CommPass357/Train-Models/models/up-80-coal-turbine/v1.0.4/exports/stl/shells/a_control_shell.stl

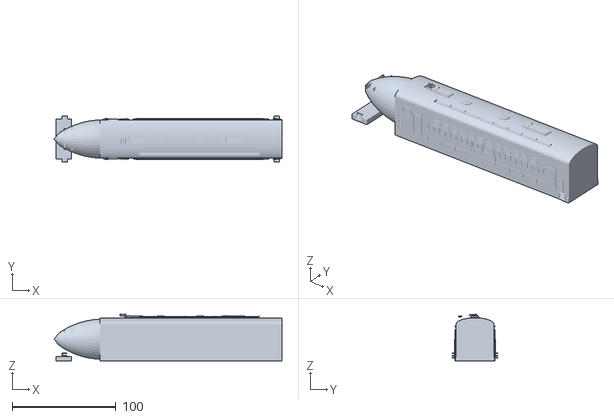
[picture p15: CAD file, 2026-04-26]
models/up-80-coal-turbine/v1.0.4/exports/stl/shells/a_control_shell.stl
219.4 x 44.0 x 45.1
