CommPass357/Train-Models/models/up-80-coal-turbine/v1.0.4/exports/stl/chassis_parts/center_turbine/center_turbine_shell_mount_boss_set.stl

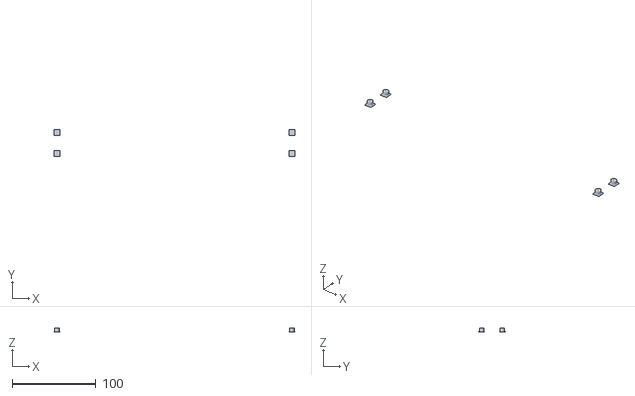
[picture p16: CAD file, 2026-04-26]
models/up-80-coal-turbine/v1.0.4/exports/stl/chassis_parts/center_turbine/center_turbine_shell_mount_boss_set.stl
287.2 x 31.7 x 4.40
