CommPass357/Train-Models/models/up-80-coal-turbine/v1.0.4/exports/stl/chassis_parts/coal_tender/coal_tender_cosmetic_sideframes.stl

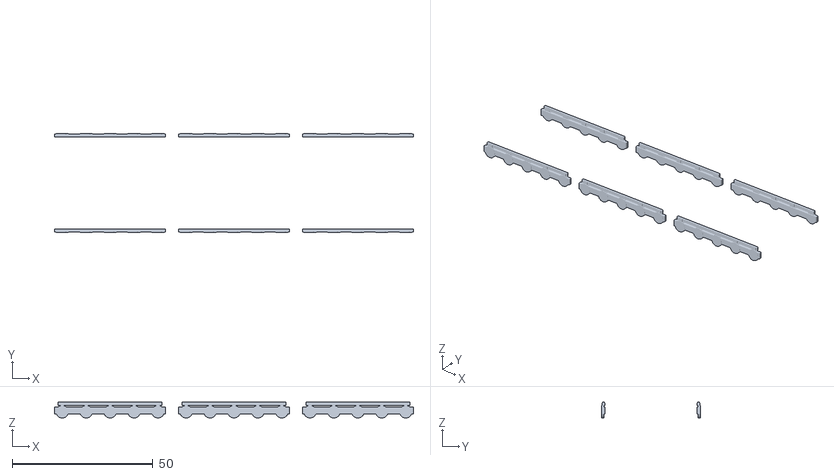
[picture p17: CAD file, 2026-04-26]
models/up-80-coal-turbine/v1.0.4/exports/stl/chassis_parts/coal_tender/coal_tender_cosmetic_sideframes.stl
127.5 x 35.0 x 5.67
