CommPass357/Train-Models/models/up-80-coal-turbine/v1.0.4/exports/stl/chassis_parts/a_control/a_control_truck_bolster_01.stl

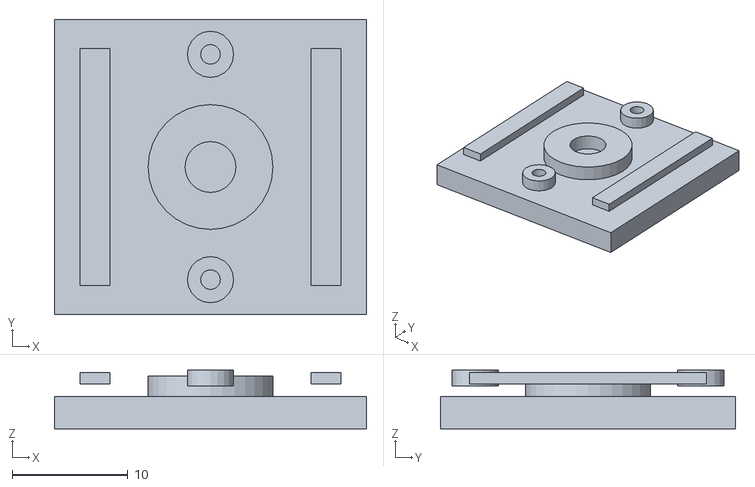
[picture p18: CAD file, 2026-04-26]
models/up-80-coal-turbine/v1.0.4/exports/stl/chassis_parts/a_control/a_control_truck_bolster_01.stl
27.0 x 25.5 x 5.10
