CommPass357/Train-Models/models/up-80-coal-turbine/v1.0.4/exports/stl/chassis_parts/coal_tender/coal_tender_wire_retainers.stl

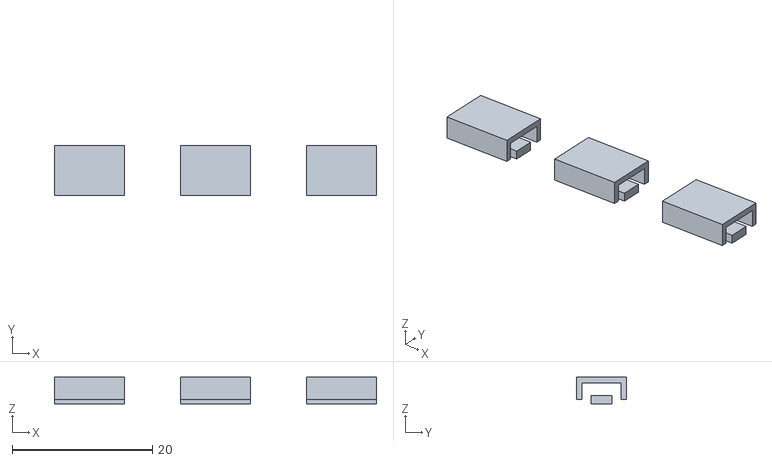
[picture p19: CAD file, 2026-04-26]
models/up-80-coal-turbine/v1.0.4/exports/stl/chassis_parts/coal_tender/coal_tender_wire_retainers.stl
46.0 x 7.20 x 3.80
