CommPass357/Train-Models/models/up-80-coal-turbine/v1.0.4/exports/stl/chassis_parts/coal_tender/coal_tender_decoder_tray.stl

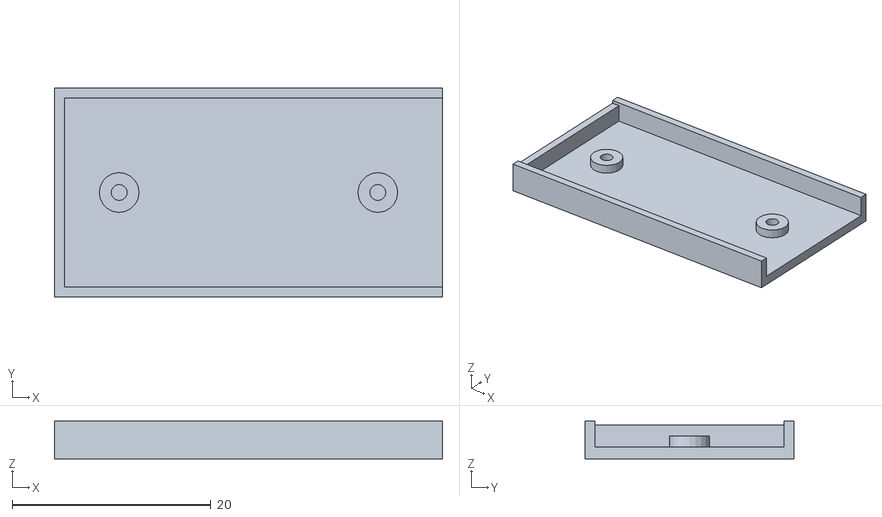
[picture p20: CAD file, 2026-04-26]
models/up-80-coal-turbine/v1.0.4/exports/stl/chassis_parts/coal_tender/coal_tender_decoder_tray.stl
39.0 x 21.0 x 3.80
