CommPass357/Train-Models/models/up-80-coal-turbine/v1.0.4/exports/stl/chassis_parts/coal_tender/coal_tender_pickup_wiper_mounts.stl

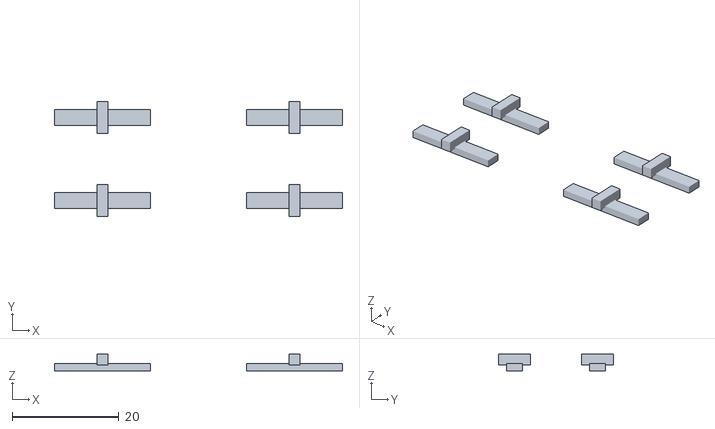
[picture p21: CAD file, 2026-04-26]
models/up-80-coal-turbine/v1.0.4/exports/stl/chassis_parts/coal_tender/coal_tender_pickup_wiper_mounts.stl
54.0 x 21.5 x 3.10
