CommPass357/Train-Models/models/up-80-coal-turbine/v1.0.4/exports/stl/chassis_parts/a_control/a_control_speaker_box.stl

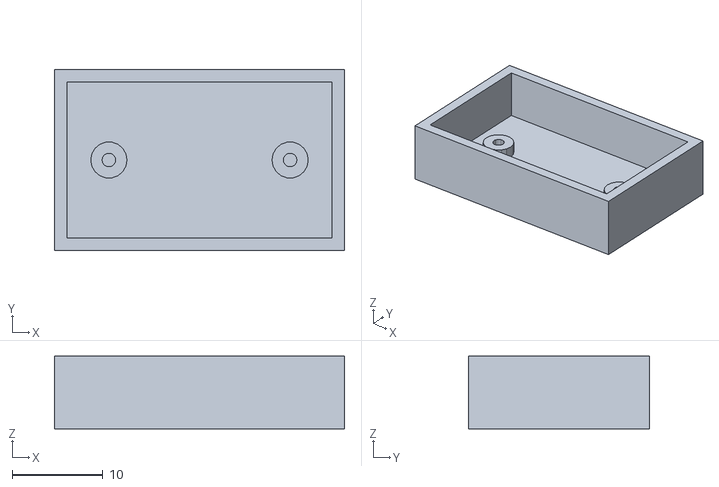
[picture p22: CAD file, 2026-04-26]
models/up-80-coal-turbine/v1.0.4/exports/stl/chassis_parts/a_control/a_control_speaker_box.stl
32.0 x 20.0 x 8.00
