CommPass357/Train-Models/models/up-80-coal-turbine/v1.0.4/exports/stl/chassis_parts/center_turbine/center_turbine_chassis_base_plate.stl

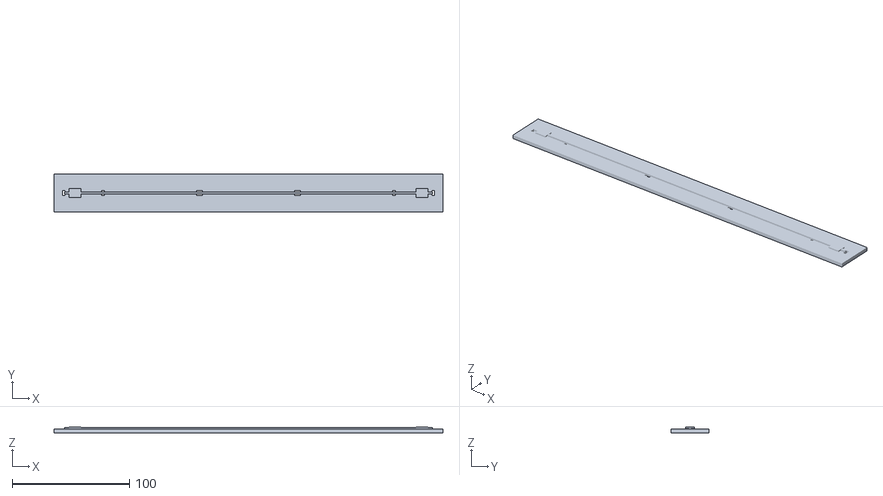
[picture p23: CAD file, 2026-04-26]
models/up-80-coal-turbine/v1.0.4/exports/stl/chassis_parts/center_turbine/center_turbine_chassis_base_plate.stl
332.0 x 32.5 x 4.80
