CommPass357/Train-Models/models/up-80-coal-turbine/v1.0.4/exports/stl/chassis_parts/coal_tender/coal_tender_optional_power_truck_adapter.stl

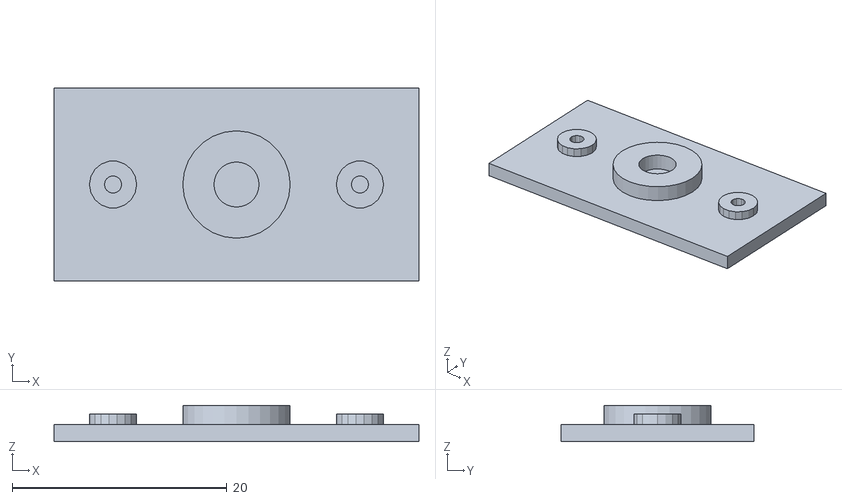
[picture p24: CAD file, 2026-04-26]
models/up-80-coal-turbine/v1.0.4/exports/stl/chassis_parts/coal_tender/coal_tender_optional_power_truck_adapter.stl
34.0 x 18.0 x 3.40
