CommPass357/Train-Models/models/up-80-coal-turbine/v1.0.4/exports/stl/chassis_parts/a_control/a_control_cosmetic_sideframes.stl

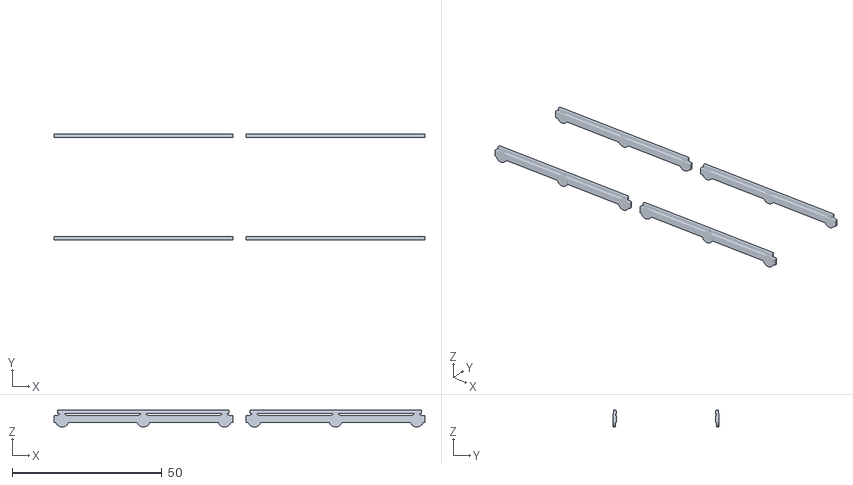
[picture p25: CAD file, 2026-04-26]
models/up-80-coal-turbine/v1.0.4/exports/stl/chassis_parts/a_control/a_control_cosmetic_sideframes.stl
123.9 x 35.5 x 5.67
