CommPass357/Train-Models/models/up-80-coal-turbine/v1.0.4/exports/stl/chassis_parts/center_turbine/center_turbine_motor_cradle.stl

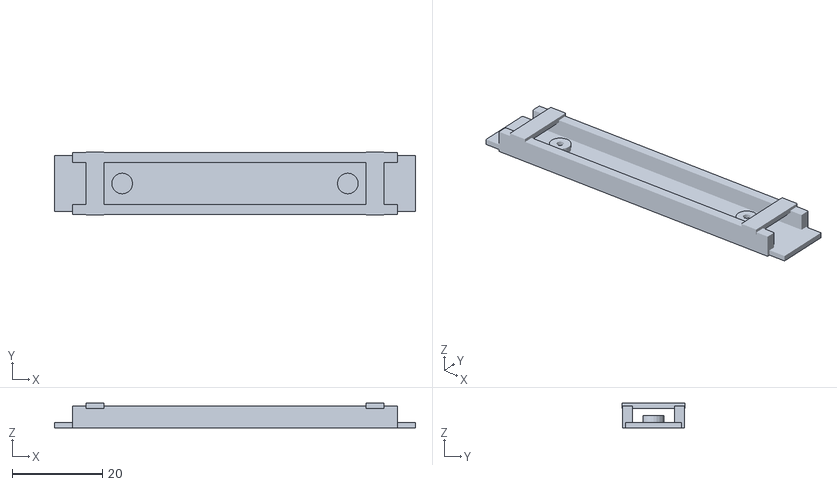
[picture p26: CAD file, 2026-04-26]
models/up-80-coal-turbine/v1.0.4/exports/stl/chassis_parts/center_turbine/center_turbine_motor_cradle.stl
80.0 x 14.0 x 5.50
