CommPass357/Train-Models/models/up-80-coal-turbine/v1.0.4/exports/stl/chassis_parts/a_control/a_control_chassis_base_plate.stl

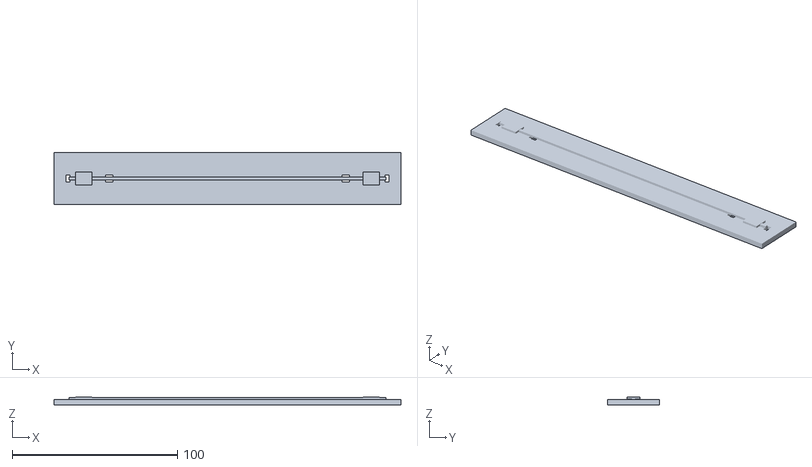
[picture p27: CAD file, 2026-04-26]
models/up-80-coal-turbine/v1.0.4/exports/stl/chassis_parts/a_control/a_control_chassis_base_plate.stl
210.0 x 31.5 x 4.80
