CommPass357/Train-Models/models/up-80-coal-turbine/v1.0.4/exports/stl/chassis_parts/center_turbine/center_turbine_cosmetic_sideframes.stl

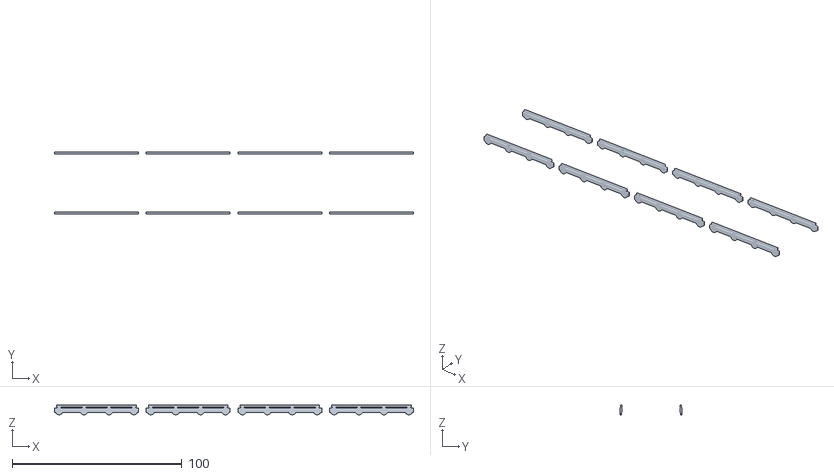
[picture p30: CAD file, 2026-04-26]
models/up-80-coal-turbine/v1.0.4/exports/stl/chassis_parts/center_turbine/center_turbine_cosmetic_sideframes.stl
211.5 x 36.5 x 5.67
