CommPass357/Train-Models/models/up-80-coal-turbine/v1.0.4/exports/stl/chassis_parts/center_turbine/center_turbine_speaker_box.stl

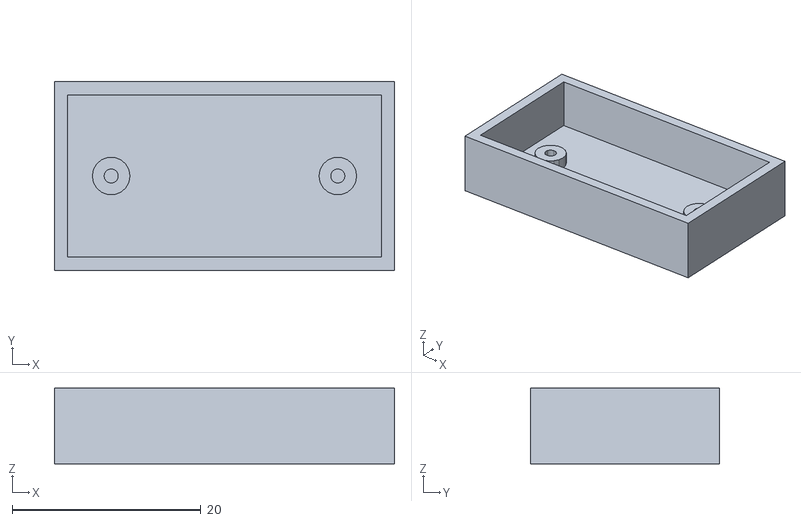
[picture p32: CAD file, 2026-04-26]
models/up-80-coal-turbine/v1.0.4/exports/stl/chassis_parts/center_turbine/center_turbine_speaker_box.stl
36.0 x 20.0 x 8.00
